alex-snigir/BlueRetro-3.3V-logic/doc/XBox 360 Controller Buttons - not supported.jpg

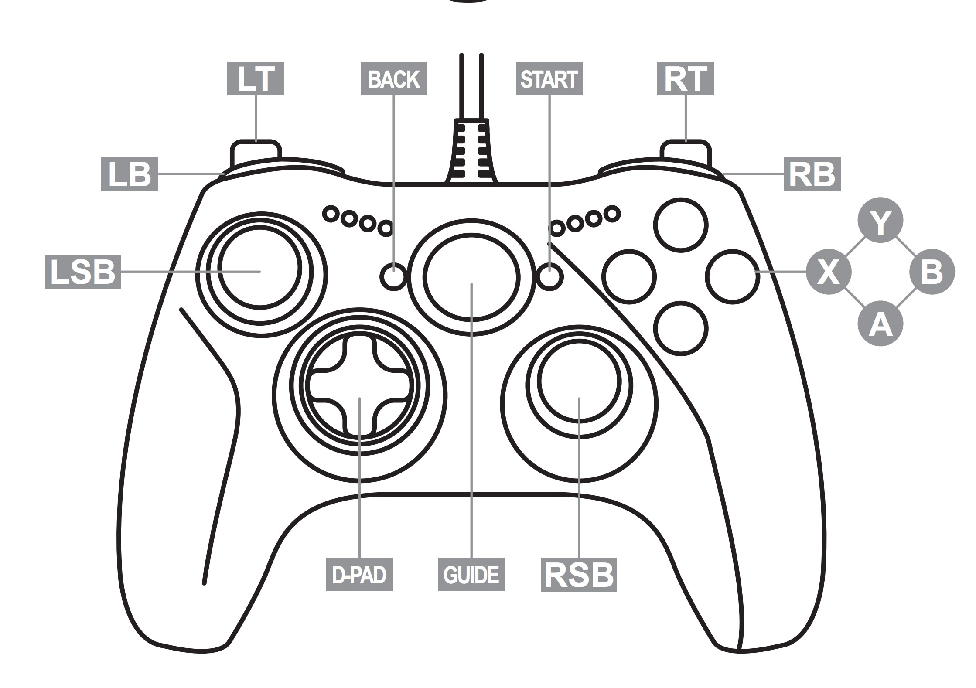
doc/XBox 360 Controller Buttons - not supported.jpg
